MartinDavidWaller/BeaconBox/Source/BeaconBox/LEDChain.h

/*
 *  LEDChain.h
 *  
 *  Author:   M.D. Waller - G0PJO
 *  Copyright (c) 2024
 */

#include <FastLED.h>

// The following manifests define the values associated with the LED chain.

#if BUILD_TYPE == BUILD_TYPE_TEST_BOARD

#define LED_CHAIN_LENGTH 25

#define LED_BEACON_FREQUENCY_14100 0
#define LED_BEACON_FREQUENCY_18110 1
#define LED_BEACON_FREQUENCY_21150 2
#define LED_BEACON_FREQUENCY_24930 3
#define LED_BEACON_FREQUENCY_28200 4

#define LED_VE8AT 5
#define LED_KH6RS 6
#define LED_W6WX 7
#define LED_4U1UN 8
#define LED_CS3B 9
#define LED_YV5B 10
#define LED_OA4B 11
#define LED_LU4AA 12
#define LED_ZS6DN 13
#define LED_5Z4B 14
#define LED_4X6TU 15
#define LED_OH2B 16
#define LED_RR90 17
#define LED_4S7B 18
#define LED_VR2B 19
#define LED_JA2IGY 20
#define LED_VK6RBP 21
#define LED_ZL6B 22

#define LED_BEACON_FIRST LED_VE8AT
#define LED_BEACON_LAST LED_ZL6B

#define LED_DATA 23
#define LED_MISC_2 24

#elif BUILD_TYPE == BUILD_TYPE_YAESU_MAP

#define LED_CHAIN_LENGTH 24

#define LED_BEACON_FREQUENCY_14100 0        // 1
#define LED_BEACON_FREQUENCY_18110 1        // 2
#define LED_BEACON_FREQUENCY_21150 2        // 3
#define LED_BEACON_FREQUENCY_24930 3        // 4
#define LED_BEACON_FREQUENCY_28200 4        // 5
#define LED_DATA 5                          // 6

#define LED_ZL6B 6                          // 7
#define LED_VK6RBP 7                        // 8
#define LED_JA2IGY 8                        // 9
#define LED_VR2B 9                          // 10
#define LED_4S7B 10                         // 11
#define LED_RR90 11                         // 12
#define LED_4X6TU 12                        // 13
#define LED_5Z4B 13                         // 14
#define LED_ZS6DN 14                        // 15
#define LED_OH2B 15                         // 16
#define LED_CS3B 16                         // 17
#define LED_VE8AT 17                        // 18
#define LED_W6WX 18                         // 19
#define LED_KH6RS 19                        // 20
#define LED_4U1UN 20                        // 21
#define LED_YV5B 21                         // 22
#define LED_OA4B 22                         // 23
#define LED_LU4AA 23                        // 24

#define LED_BEACON_FIRST LED_ZL6B
#define LED_BEACON_LAST LED_LU4AA

#else

  #error BUILD_TYPE - Unrecognised value.
#endif

#define LED_PIN 14

#define LED_BEACON_FREQUENCY_FIRST LED_BEACON_FREQUENCY_14100
#define LED_BEACON_FREQUENCY_LAST LED_BEACON_FREQUENCY_28200

// Define routines and functions

extern void ledChainSetUp();
extern void ledChainBlinkAll();
extern void ledSetIndexColour(int index,CRGB colour);
extern void ledTurnOffAllFrequencyLeds();
extern void ledTurnOffAllBeaconLeds();
extern void ledBrightness(uint8_t newBrightness);
