MartinDavidWaller/BeaconBox/Source/BeaconBox/Animation.h

/*
 *  Animation.h
 *  
 *  Author:   M.D. Waller - G0PJO
 *  Copyright (c) 2024
 */

// Define routines and functions

void animationSetUp(void _modeChangeHandler(bool manualEvent));
void animationStart();
void animationAnimate();
void animationManualEvent();

 
